kitkat9525/MINI/3D Modeling/Modeling2.png

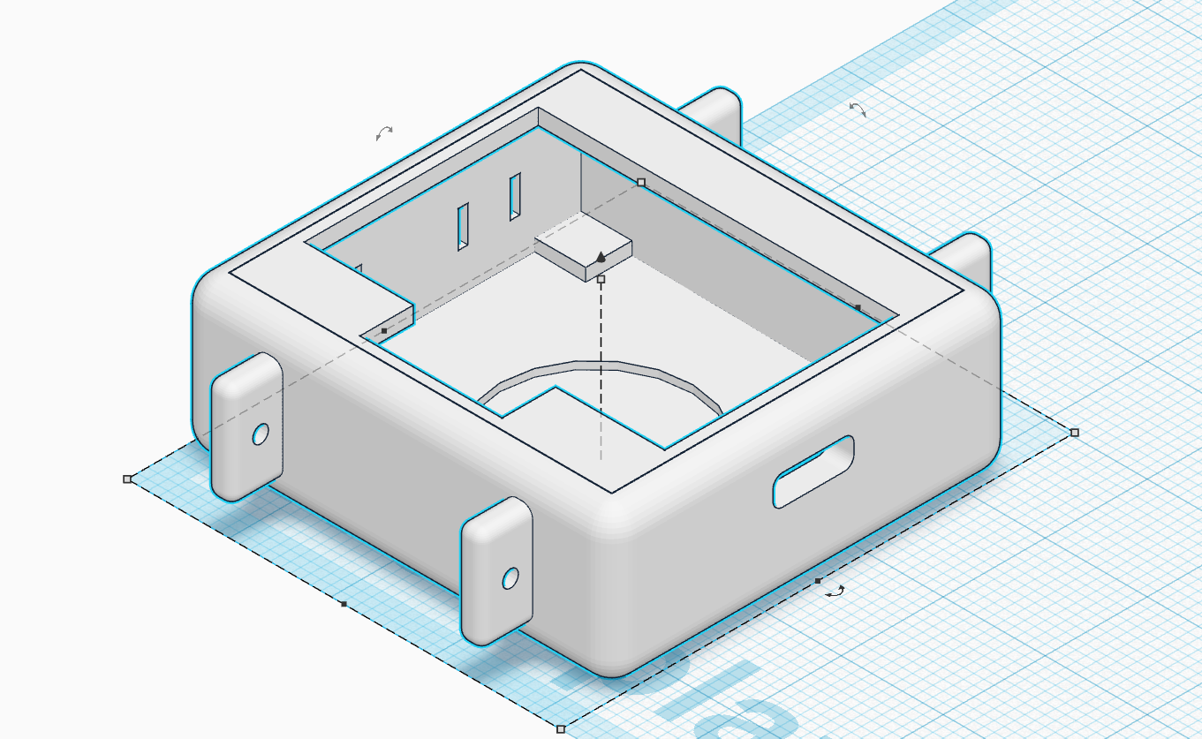
3D Modeling/Modeling2.png
