kitkat9525/MINI/PCBArtwork/PCB_3D_View.png

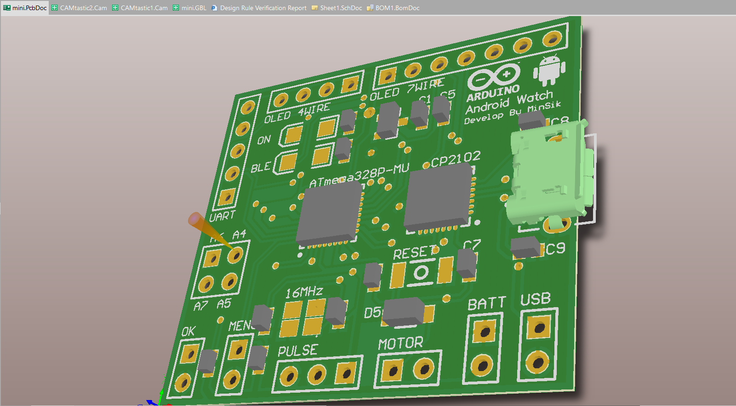
PCBArtwork/PCB_3D_View.png
