kitkat9525/MINI/PCBArtwork/PCB_Bottom_Layer.png

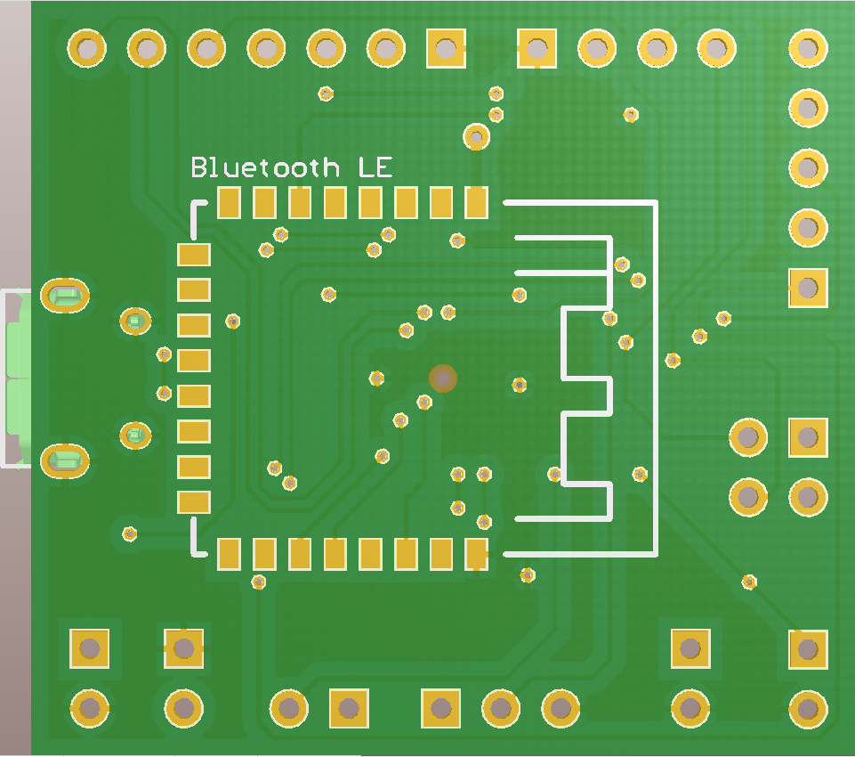
PCBArtwork/PCB_Bottom_Layer.png
