kitkat9525/MINI/Reference Circuit/CP2102_USB_To_UART.png

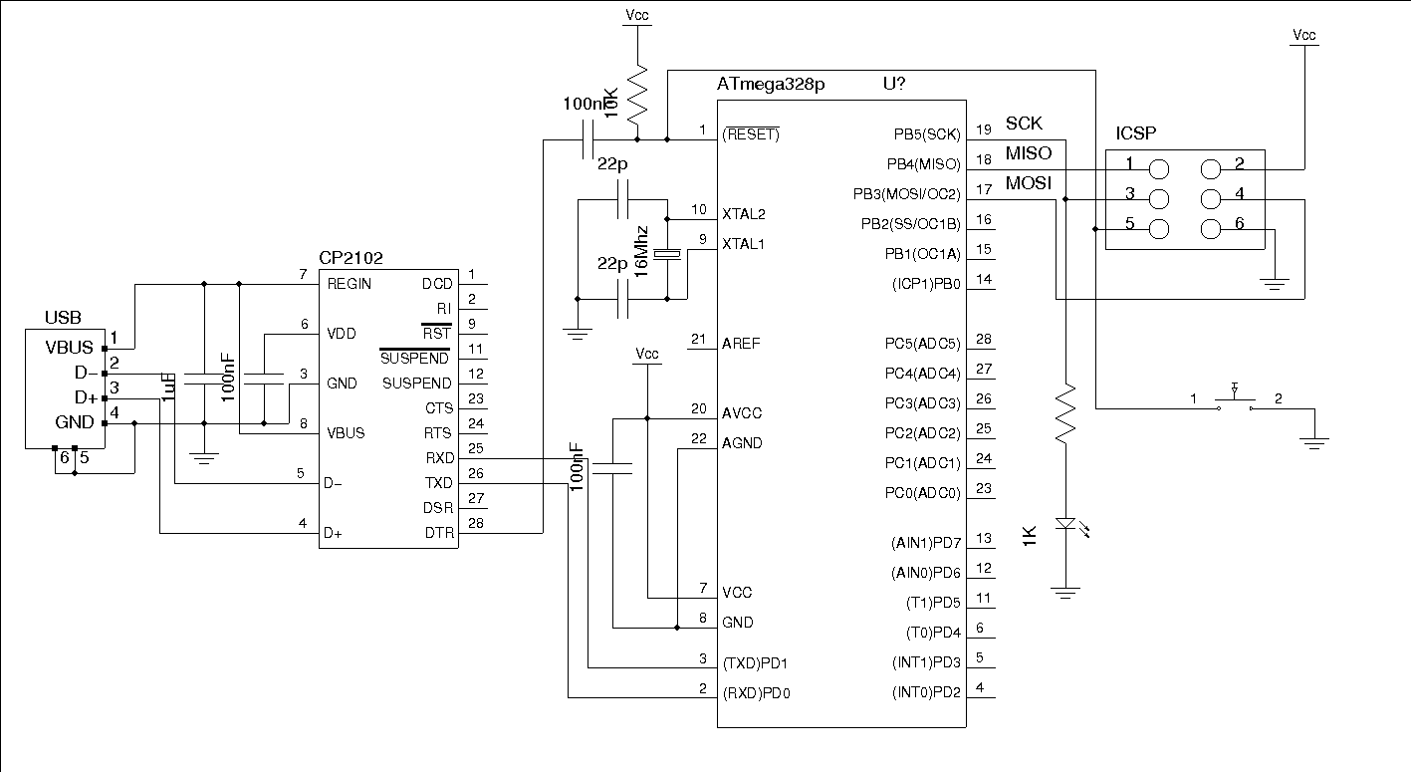
Reference Circuit/CP2102_USB_To_UART.png
