kitkat9525/MINI/Reference Circuit/TP4056-1A Micro USB Li-ION Battery Charger Module with Protection.jpg

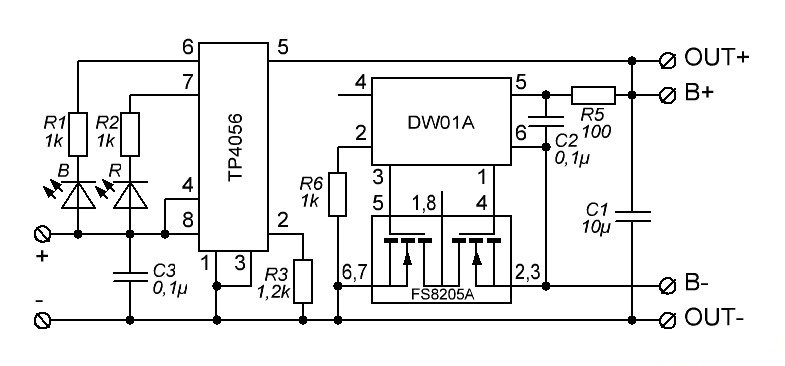
Reference Circuit/TP4056-1A Micro USB Li-ION Battery Charger Module with Protection.jpg
