kitkat9525/MINI/Arduino/Mini/bitmap.h

#ifndef BITMAP_H_
#define BITMAP_H_

const uint8_t android[] PROGMEM = {
    0x0,0x0,0x0,0x0,0x0,0x0,0x0,0x0,0x0,0x0,0x0,0x0,0x0,0x0,0x0,0x0,
    0x0,0x0,0x0,0x0,0x0,0x0,0x0,0x0,0x0,0x0,0x0,0x0,0x0,0x0,0x0,0x0,
    0x0,0x0,0x0,0x0,0x0,0x0,0x0,0x0,0x0,0x0,0x0,0x0,0x0,0x0,0x0,0x0,
    0x0,0x0,0x0,0x0,0x0,0x0,0x0,0x0,0x0,0x0,0x0,0x0,0x0,0x0,0x0,0x0,
    0x0,0x0,0x0,0x0,0x0,0x0,0x0,0x0,0x0,0x0,0x0,0x0,0x0,0x0,0x0,0x0,
    0x0,0x0,0x0,0x0,0x0,0x0,0x0,0x0,0x0,0x2,0x0,0x0,0x0,0x0,0x0,0x0,
    0x0,0x0,0x0,0x0,0x0,0x0,0x10,0x0,0x0,0x6,0x0,0x0,0x0,0x0,0x0,0x0,
    0x0,0x0,0x0,0x0,0x0,0x0,0x8,0x0,0x0,0x4,0x0,0x0,0x0,0x0,0x0,0x0,
    0x0,0x0,0x0,0x0,0x0,0x0,0x4,0x0,0x0,0x8,0x0,0x0,0x0,0x0,0x0,0x0,
    0x0,0x0,0x0,0x0,0x0,0x0,0x6,0xff,0xff,0x90,0x0,0x0,0x0,0x0,0x0,0x0,
    0x0,0x0,0x0,0x0,0x0,0x0,0x7,0xff,0xff,0xf0,0x0,0x0,0x0,0x0,0x0,0x0,
    0x0,0x0,0x0,0x0,0x0,0x0,0x1f,0xff,0xff,0xfe,0x0,0x0,0x0,0x0,0x0,0x0,
    0x0,0x0,0x0,0x0,0x0,0x0,0x7f,0xff,0xff,0xff,0x0,0x0,0x0,0x0,0x0,0x0,
    0x0,0x0,0x0,0x0,0x0,0x0,0xff,0xff,0xff,0xff,0xc0,0x0,0x0,0x0,0x0,0x0,
    0x0,0x0,0x0,0x0,0x0,0x3,0xf8,0xff,0xff,0xcf,0xe0,0x0,0x0,0x0,0x0,0x0,
    0x0,0x0,0x0,0x0,0x0,0x7,0xf8,0x7f,0xff,0x87,0xf0,0x0,0x0,0x0,0x0,0x0,
    0x0,0x0,0x0,0x0,0x0,0xf,0xf8,0xff,0xff,0xcf,0xf8,0x0,0x0,0x0,0x0,0x0,
    0x0,0x0,0x0,0x0,0x0,0xf,0xff,0xff,0xff,0xff,0xfc,0x0,0x0,0x0,0x0,0x0,
    0x0,0x0,0x0,0x0,0x0,0x1f,0xff,0xff,0xff,0xff,0xfc,0x0,0x0,0x0,0x0,0x0,
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
    0x0,0x3,0xf0,0x0,0x0,0x0,0x0,0x0,
    0x0,0x1,0xf8,0x0,0x0,0x0,0x0,0x0,
    0x0,0x1,0xfc,0x0,0x0,0x0,0x0,0x0,
    0x0,0x0,0xfe,0x0,0x0,0x0,0x0,0x0,
    0x0,0x0,0x7f,0x0,0x0,0x0,0x0,0x0,
    0x0,0x0,0x7f,0x0,0x0,0x0,0x0,0x0,
    0x0,0x0,0x3f,0xc0,0x0,0x0,0x0,0x0,
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
};

#endif /* BITMAP_H_ */
/*
    >>> Before compiling: Please remove comment from the constructor of the 
    >>> connected graphics display (see below).
    
    Universal 8bit Graphics Library, https://github.com/olikraus/u8glib/
    
    Copyright (c) 2012, olikraus@gmail.com
    All rights reserved.
    
    Redistribution and use in source and binary forms, with or without modification, 
    are permitted provided that the following conditions are met:
    
    * Redistributions of source code must retain the above copyright notice, this list 
      of conditions and the following disclaimer.
      
    * Redistributions in binary form must reproduce the above copyright notice, this 
      list of conditions and the following disclaimer in the documentation and/or other 
      materials provided with the distribution.
    
    THIS SOFTWARE IS PROVIDED BY THE COPYRIGHT HOLDERS AND 
    CONTRIBUTORS "AS IS" AND ANY EXPRESS OR IMPLIED WARRANTIES, 
    INCLUDING, BUT NOT LIMITED TO, THE IMPLIED WARRANTIES OF 
    MERCHANTABILITY AND FITNESS FOR A PARTICULAR PURPOSE ARE 
    DISCLAIMED. IN NO EVENT SHALL THE COPYRIGHT HOLDER OR 
    CONTRIBUTORS BE LIABLE FOR ANY DIRECT, INDIRECT, INCIDENTAL, 
    SPECIAL, EXEMPLARY, OR CONSEQUENTIAL DAMAGES (INCLUDING, BUT 
    NOT LIMITED TO, PROCUREMENT OF SUBSTITUTE GOODS OR SERVICES; 
    LOSS OF USE, DATA, OR PROFITS; OR BUSINESS INTERRUPTION) HOWEVER 
    CAUSED AND ON ANY THEORY OF LIABILITY, WHETHER IN CONTRACT, 
    STRICT LIABILITY, OR TORT (INCLUDING NEGLIGENCE OR OTHERWISE) 
    ARISING IN ANY WAY OUT OF THE USE OF THIS SOFTWARE, EVEN IF 
    ADVISED OF THE POSSIBILITY OF SUCH DAMAGE.
*/

// setup u8g object, please remove comment from one of the following constructor calls
// IMPORTANT NOTE: The following list is incomplete. The complete list of supported 
// devices with all constructor calls is here: https://github.com/olikraus/u8glib/wiki/device
//U8GLIB_NHD27OLED_BW u8g(13, 11, 10, 9);  // SPI Com: SCK = 13, MOSI = 11, CS = 10, A0 = 9
//U8GLIB_NHD27OLED_2X_BW u8g(13, 11, 10, 9);  // SPI Com: SCK = 13, MOSI = 11, CS = 10, A0 = 9
//U8GLIB_NHD27OLED_GR u8g(13, 11, 10, 9); // SPI Com: SCK = 13, MOSI = 11, CS = 10, A0 = 9
//U8GLIB_NHD27OLED_2X_GR u8g(13, 11, 10, 9);  // SPI Com: SCK = 13, MOSI = 11, CS = 10, A0 = 9
//U8GLIB_NHD31OLED_BW u8g(13, 11, 10, 9); // SPI Com: SCK = 13, MOSI = 11, CS = 10, A0 = 9
//U8GLIB_NHD31OLED_2X_BW u8g(13, 11, 10, 9);  // SPI Com: SCK = 13, MOSI = 11, CS = 10, A0 = 9
//U8GLIB_NHD31OLED_GR u8g(13, 11, 10, 9); // SPI Com: SCK = 13, MOSI = 11, CS = 10, A0 = 9
//U8GLIB_NHD31OLED_2X_GR u8g(13, 11, 10, 9);  // SPI Com: SCK = 13, MOSI = 11, CS = 10, A0 = 9
//U8GLIB_DOGS102 u8g(13, 11, 10, 9, 8);   // SPI Com: SCK = 13, MOSI = 11, CS = 10, A0 = 9
//U8GLIB_DOGM132 u8g(13, 11, 10, 9);    // SPI Com: SCK = 13, MOSI = 11, CS = 10, A0 = 9
//U8GLIB_DOGM128 u8g(13, 11, 10, 9);    // SPI Com: SCK = 13, MOSI = 11, CS = 10, A0 = 9
//U8GLIB_DOGM128_2X u8g(13, 11, 10, 9);   // SPI Com: SCK = 13, MOSI = 11, CS = 10, A0 = 9
//U8GLIB_ST7920_128X64_1X u8g(8, 9, 10, 11, 4, 5, 6, 7, 18, 17, 16);   // 8Bit Com: D0..D7: 8,9,10,11,4,5,6,7 en=18, di=17,rw=16
//U8GLIB_ST7920_128X64_4X u8g(8, 9, 10, 11, 4, 5, 6, 7, 18, 17, 16);   // 8Bit Com: D0..D7: 8,9,10,11,4,5,6,7 en=18, di=17,rw=16
//U8GLIB_ST7920_128X64_1X u8g(18, 16, 17);  // SPI Com: SCK = en = 18, MOSI = rw = 16, CS = di = 17
//U8GLIB_ST7920_128X64_4X u8g(18, 16, 17);  // SPI Com: SCK = en = 18, MOSI = rw = 16, CS = di = 17
//U8GLIB_ST7920_192X32_1X u8g(8, 9, 10, 11, 4, 5, 6, 7, 18, 17, 16);   // 8Bit Com: D0..D7: 8,9,10,11,4,5,6,7 en=18, di=17,rw=16
//U8GLIB_ST7920_192X32_4X u8g(8, 9, 10, 11, 4, 5, 6, 7, 18, 17, 16);   // 8Bit Com: D0..D7: 8,9,10,11,4,5,6,7 en=18, di=17,rw=16
//U8GLIB_ST7920_192X32_1X u8g(18, 16, 17);  // SPI Com: SCK = en = 18, MOSI = rw = 16, CS = di = 17
//U8GLIB_ST7920_192X32_4X u8g(18, 16, 17);  // SPI Com: SCK = en = 18, MOSI = rw = 16, CS = di = 17
//U8GLIB_ST7920_192X32_1X u8g(13, 11, 10);  // SPI Com: SCK = en = 13, MOSI = rw = 11, CS = di = 10
//U8GLIB_ST7920_192X32_4X u8g(10);    // SPI Com: SCK = en = 13, MOSI = rw = 11, CS = di = 10, HW SPI
//U8GLIB_ST7920_202X32_1X u8g(8, 9, 10, 11, 4, 5, 6, 7, 18, 17, 16);   // 8Bit Com: D0..D7: 8,9,10,11,4,5,6,7 en=18, di=17,rw=16
//U8GLIB_ST7920_202X32_4X u8g(8, 9, 10, 11, 4, 5, 6, 7, 18, 17, 16);   // 8Bit Com: D0..D7: 8,9,10,11,4,5,6,7 en=18, di=17,rw=16
//U8GLIB_ST7920_202X32_1X u8g(18, 16, 17);  // SPI Com: SCK = en = 18, MOSI = rw = 16, CS = di = 17
//U8GLIB_ST7920_202X32_4X u8g(18, 16, 17);  // SPI Com: SCK = en = 18, MOSI = rw = 16, CS = di = 17
//U8GLIB_LM6059 u8g(13, 11, 10, 9);   // SPI Com: SCK = 13, MOSI = 11, CS = 10, A0 = 9
//U8GLIB_LM6063 u8g(13, 11, 10, 9);   // SPI Com: SCK = 13, MOSI = 11, CS = 10, A0 = 9
//U8GLIB_DOGXL160_BW u8g(10, 9);    // SPI Com: SCK = 13, MOSI = 11, CS = 10, A0 = 9
//U8GLIB_DOGXL160_GR u8g(13, 11, 10, 9);  // SPI Com: SCK = 13, MOSI = 11, CS = 10, A0 = 9
//U8GLIB_DOGXL160_2X_BW u8g(13, 11, 10, 9); // SPI Com: SCK = 13, MOSI = 11, CS = 10, A0 = 9
//U8GLIB_DOGXL160_2X_GR u8g(13, 11, 10, 9); // SPI Com: SCK = 13, MOSI = 11, CS = 10, A0 = 9
//U8GLIB_PCD8544 u8g(13, 11, 10, 9, 8);   // SPI Com: SCK = 13, MOSI = 11, CS = 10, A0 = 9, Reset = 8
//U8GLIB_PCF8812 u8g(13, 11, 10, 9, 8);   // SPI Com: SCK = 13, MOSI = 11, CS = 10, A0 = 9, Reset = 8
//U8GLIB_KS0108_128 u8g(8, 9, 10, 11, 4, 5, 6, 7, 18, 14, 15, 17, 16);    // 8Bit Com: D0..D7: 8,9,10,11,4,5,6,7 en=18, cs1=14, cs2=15,di=17,rw=16
//U8GLIB_LC7981_160X80 u8g(8, 9, 10, 11, 4, 5, 6, 7,  18, 14, 15, 17, 16);  // 8Bit Com: D0..D7: 8,9,10,11,4,5,6,7 en=18, cs=14 ,di=15,rw=17, reset = 16
//U8GLIB_LC7981_240X64 u8g(8, 9, 10, 11, 4, 5, 6, 7,  18, 14, 15, 17, 16);  // 8Bit Com: D0..D7: 8,9,10,11,4,5,6,7 en=18, cs=14 ,di=15,rw=17, reset = 16
//U8GLIB_LC7981_240X128 u8g(8, 9, 10, 11, 4, 5, 6, 7,  18, 14, 15, 17, 16);   // 8Bit Com: D0..D7: 8,9,10,11,4,5,6,7 en=18, cs=14 ,di=15,rw=17, reset = 16
//U8GLIB_ILI9325D_320x240 u8g(18,17,19,U8G_PIN_NONE,16 );       // 8Bit Com: D0..D7: 0,1,2,3,4,5,6,7 en=wr=18, cs=17, rs=19, rd=U8G_PIN_NONE, reset = 16
//U8GLIB_SBN1661_122X32 u8g(8,9,10,11,4,5,6,7,14,15, 17, U8G_PIN_NONE, 16);   // 8Bit Com: D0..D7: 8,9,10,11,4,5,6,7 cs1=14, cs2=15,di=17,rw=16,reset = 16
//U8GLIB_SSD1306_128X64 u8g(13, 11, 10, 9); // SW SPI Com: SCK = 13, MOSI = 11, CS = 10, A0 = 9
//U8GLIB_SSD1306_128X64 u8g(4, 5, 6, 7);  // SW SPI Com: SCK = 4, MOSI = 5, CS = 6, A0 = 7 (new white HalTec OLED)
//U8GLIB_SSD1306_128X64 u8g(10, 9);   // HW SPI Com: CS = 10, A0 = 9 (Hardware Pins are  SCK = 13 and MOSI = 11)
//U8GLIB_SSD1306_128X64 u8g(U8G_I2C_OPT_NONE|U8G_I2C_OPT_DEV_0);  // I2C / TWI 
//U8GLIB_SSD1306_128X64 u8g(U8G_I2C_OPT_DEV_0|U8G_I2C_OPT_NO_ACK|U8G_I2C_OPT_FAST); // Fast I2C / TWI 
//U8GLIB_SSD1306_128X64 u8g(U8G_I2C_OPT_NO_ACK);  // Display which does not send AC
//U8GLIB_SSD1306_ADAFRUIT_128X64 u8g(13, 11, 10, 9);  // SW SPI Com: SCK = 13, MOSI = 11, CS = 10, A0 = 9
//U8GLIB_SSD1306_ADAFRUIT_128X64 u8g(10, 9);    // HW SPI Com: CS = 10, A0 = 9 (Hardware Pins are  SCK = 13 and MOSI = 11)
//U8GLIB_SSD1306_128X32 u8g(13, 11, 10, 9); // SW SPI Com: SCK = 13, MOSI = 11, CS = 10, A0 = 9
//U8GLIB_SSD1306_128X32 u8g(10, 9);             // HW SPI Com: CS = 10, A0 = 9 (Hardware Pins are  SCK = 13 and MOSI = 11)
//U8GLIB_SSD1306_128X32 u8g(U8G_I2C_OPT_NONE);  // I2C / TWI 
//U8GLIB_SSD1306_64X48 u8g(13, 11, 10, 9);  // SW SPI Com: SCK = 13, MOSI = 11, CS = 10, A0 = 9
//U8GLIB_SSD1306_64X48 u8g(10, 9);             // HW SPI Com: CS = 10, A0 = 9 (Hardware Pins are  SCK = 13 and MOSI = 11)
//U8GLIB_SSD1306_64X48 u8g(U8G_I2C_OPT_NONE); // I2C / TWI 
//U8GLIB_SH1106_128X64 u8g(13, 11, 10, 9);  // SW SPI Com: SCK = 13, MOSI = 11, CS = 10, A0 = 9
//U8GLIB_SH1106_128X64 u8g(4, 5, 6, 7); // SW SPI Com: SCK = 4, MOSI = 5, CS = 6, A0 = 7 (new blue HalTec OLED)
//U8GLIB_SH1106_128X64 u8g(U8G_I2C_OPT_NONE); // I2C / TWI 
//U8GLIB_SH1106_128X64 u8g(U8G_I2C_OPT_DEV_0|U8G_I2C_OPT_FAST); // Dev 0, Fast I2C / TWI
//U8GLIB_SH1106_128X64 u8g(U8G_I2C_OPT_NO_ACK); // Display which does not send ACK
//U8GLIB_SSD1309_128X64 u8g(13, 11, 10, 9); // SPI Com: SCK = 13, MOSI = 11, CS = 10, A0 = 9
//U8GLIB_SSD1327_96X96_GR u8g(U8G_I2C_OPT_NONE);  // I2C
//U8GLIB_SSD1327_96X96_2X_GR u8g(U8G_I2C_OPT_NONE); // I2C
//U8GLIB_UC1611_DOGM240 u8g(U8G_I2C_OPT_NONE);  // I2C
//U8GLIB_UC1611_DOGM240 u8g(13, 11, 10, 9); // SW SPI Com: SCK = 13, MOSI = 11, CS = 10, A0 = 9
//U8GLIB_UC1611_DOGM240 u8g(10, 9);   // HW SPI Com: CS = 10, A0 = 9 (Hardware Pins are  SCK = 13 and MOSI = 11)
//U8GLIB_UC1611_DOGM240 u8g(10, 9);   // HW SPI Com: CS = 10, A0 = 9 (Hardware Pins are  SCK = 13 and MOSI = 11)
//U8GLIB_UC1611_DOGM240 u8g(8, 9, 10, 11, 4, 5, 6, 7, 18, 3, 17, 16);   // 8Bit Com: D0..D7: 8,9,10,11,4,5,6,7 en=18, cs=3, di/a0=17,rw=16
//U8GLIB_UC1611_DOGXL240 u8g(U8G_I2C_OPT_NONE); // I2C
//U8GLIB_UC1611_DOGXL240 u8g(13, 11, 10, 9);  // SW SPI Com: SCK = 13, MOSI = 11, CS = 10, A0 = 9
//U8GLIB_UC1611_DOGXL240 u8g(10, 9);    // HW SPI Com: CS = 10, A0 = 9 (Hardware Pins are  SCK = 13 and MOSI = 11)
//U8GLIB_UC1611_DOGXL240 u8g(8, 9, 10, 11, 4, 5, 6, 7, 18, 3, 17, 16);   // 8Bit Com: D0..D7: 8,9,10,11,4,5,6,7 en=18, cs=3, di/a0=17,rw=16
//U8GLIB_NHD_C12864 u8g(13, 11, 10, 9, 8);  // SPI Com: SCK = 13, MOSI = 11, CS = 10, A0 = 9, RST = 8
//U8GLIB_NHD_C12832 u8g(13, 11, 10, 9, 8);  // SPI Com: SCK = 13, MOSI = 11, CS = 10, A0 = 9, RST = 8
//U8GLIB_LD7032_60x32 u8g(13, 11, 10, 9, 8);  // SPI Com: SCK = 13, MOSI = 11, CS = 10, A0 = 9, RST = 8
//U8GLIB_LD7032_60x32 u8g(11, 12, 9, 10, 8);  // SPI Com: SCK = 11, MOSI = 12, CS = 9, A0 = 10, RST = 8  (SW SPI Nano Board)
//U8GLIB_UC1608_240X64 u8g(13, 11, 10, 9, 8); // SW SPI Com: SCK = 13, MOSI = 11, CS = 10, A0 = 9, RST = 8
//U8GLIB_UC1608_240X64_2X u8g(13, 11, 10, 9, 8);  // SW SPI Com: SCK = 13, MOSI = 11, CS = 10, A0 = 9, RST = 8
//U8GLIB_UC1608_240X64 u8g(10, 9, 8); // HW SPI Com: SCK = 13, MOSI = 11, CS = 10, A0 = 9, RST = 8
//U8GLIB_UC1608_240X64_2X u8g(10, 9, 8);  // HW SPI Com: SCK = 13, MOSI = 11, CS = 10, A0 = 9, RST = 8
//U8GLIB_UC1608_240X u8g(13, 11, 10, 9, 8); // SW SPI Com: SCK = 13, MOSI = 11, CS = 10, A0 = 9, RST = 8
//U8GLIB_UC1608_240X64_2X u8g(13, 11, 10, 9, 8);  // SW SPI Com: SCK = 13, MOSI = 11, CS = 10, A0 = 9, RST = 8
//U8GLIB_UC1608_240X64 u8g(10, 9, 8); // HW SPI Com: SCK = 13, MOSI = 11, CS = 10, A0 = 9, RST = 8
//U8GLIB_UC1608_240X64_2X u8g(10, 9, 8);  // HW SPI Com: SCK = 13, MOSI = 11, CS = 10, A0 = 9, RST = 8
//U8GLIB_T6963_240X128 u8g(8, 9, 10, 11, 4, 5, 6, 7, 14, 15, 17, 18, 16); // 8Bit Com: D0..D7: 8,9,10,11,4,5,6,7, cs=14, a0=15, wr=17, rd=18, reset=16
//U8GLIB_T6963_128X128 u8g(8, 9, 10, 11, 4, 5, 6, 7, 14, 15, 17, 18, 16); // 8Bit Com: D0..D7: 8,9,10,11,4,5,6,7, cs=14, a0=15, wr=17, rd=18, reset=16
//U8GLIB_T6963_240X64 u8g(8, 9, 10, 11, 4, 5, 6, 7, 14, 15, 17, 18, 16); // 8Bit Com: D0..D7: 8,9,10,11,4,5,6,7, cs=14, a0=15, wr=17, rd=18, reset=16
//U8GLIB_T6963_128X64 u8g(8, 9, 10, 11, 4, 5, 6, 7, 14, 15, 17, 18, 16); // 8Bit Com: D0..D7: 8,9,10,11,4,5,6,7, cs=14, a0=15, wr=17, rd=18, reset=16
//U8GLIB_HT1632_24X16 u8g(3, 2, 4);   // WR = 3, DATA = 2, CS = 4
//U8GLIB_SSD1351_128X128_332 u8g(13, 11, 8, 9, 7); // Arduino UNO: SW SPI Com: SCK = 13, MOSI = 11, CS = 8, A0 = 9, RESET = 7 (http://electronics.ilsoft.co.uk/ArduinoShield.aspx)
//U8GLIB_SSD1351_128X128_332 u8g(76, 75, 8, 9, 7); // Arduino DUE: SW SPI Com: SCK = 13, MOSI = 11, CS = 8, A0 = 9, RESET = 7 (http://electronics.ilsoft.co.uk/ArduinoShield.aspx)
//U8GLIB_SSD1351_128X128_332 u8g(8, 9, 7); // Arduino: HW SPI Com: SCK = 13, MOSI = 11, CS = 8, A0 = 9, RESET = 7 (http://electronics.ilsoft.co.uk/ArduinoShield.aspx)
//U8GLIB_SSD1351_128X128_HICOLOR u8g(76, 75, 8, 9, 7); // Arduino DUE, SW SPI Com: SCK = 76, MOSI = 75, CS = 8, A0 = 9, RESET = 7 (http://electronics.ilsoft.co.uk/ArduinoShield.aspx)
//U8GLIB_SSD1351_128X128_HICOLOR u8g(8, 9, 7); // Arduino, HW SPI Com: SCK = 76, MOSI = 75, CS = 8, A0 = 9, RESET = 7 (http://electronics.ilsoft.co.uk/ArduinoShield.aspx)
//U8GLIB_SSD1351_128X128GH_332 u8g(8, 9, 7); // Arduino, HW SPI Com: SCK = 76, MOSI = 75, CS = 8, A0 = 9, RESET = 7 (Freetronics OLED)
//U8GLIB_SSD1351_128X128GH_HICOLOR u8g(8, 9, 7); // Arduino, HW SPI Com: SCK = 76, MOSI = 75, CS = 8, A0 = 9, RESET = 7 (Freetronics OLED)
